benbrandt22/TeamSpot/src/firmware/src/pins.py

import board

# RP2040-Zero board members: (dir(board))
# ['__class__', '__name__', 'A0', 'A1', 'A2', 'A3', 'GP0', 'GP1', 'GP10', 'GP11', 'GP12', 'GP13', 'GP14', 'GP15', 'GP16', 'GP17', 'GP18', 'GP19', 'GP2', 'GP20', 'GP21', 'GP22', 'GP23', 'GP24', 'GP25', 'GP26', 'GP26_A0', 'GP27', 'GP27_A1', 'GP28', 'GP28_A2', 'GP29', 'GP29_A3', 'GP3', 'GP4', 'GP5', 'GP6', 'GP7', 'GP8', 'GP9', 'NEOPIXEL', 'RX', 'TX', 'UART', '__dict__', 'board_id']

BUTTON_PIN = board.GP27
PIXEL_PIN  = board.GP3
